mitchellcairns/joyRGB/source/config.h

// USER PREFERENCES STRUCTURE
// ----------------
typedef struct 
{
  byte saved = 0;
  byte brightness;
  byte colorMode;
  byte rainbowTime;
  byte hue;
  byte saturation;
  byte presetSelection;
  bool displayMode;
} UserPreference;
